ra0sms/nano-server/pics/nano-server-web-2-tile.jpg

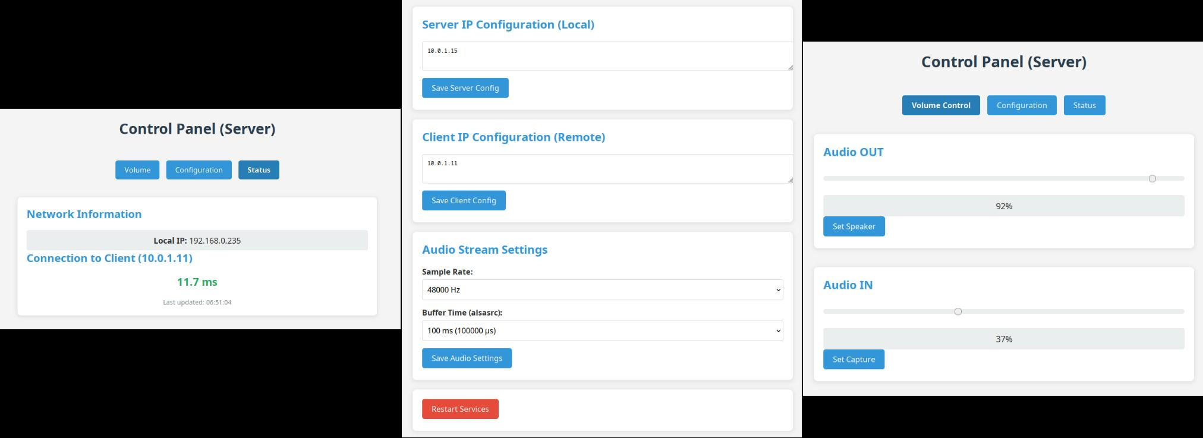
pics/nano-server-web-2-tile.jpg
