ra0sms/nano-server/pics/nano_server_3d.png

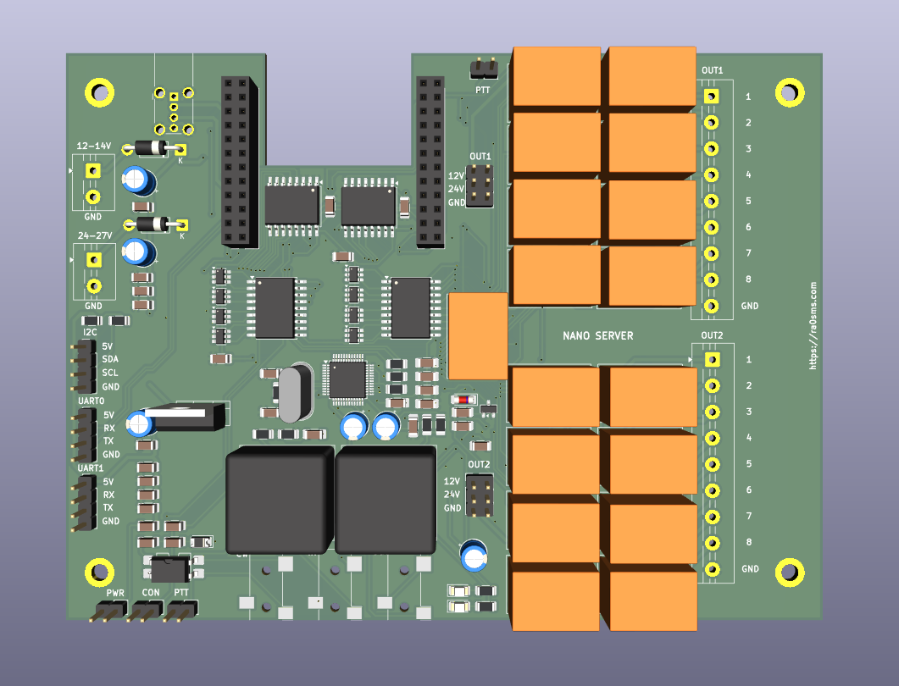
pics/nano_server_3d.png
