ra0sms/nano-server/pics/out-2.jpg

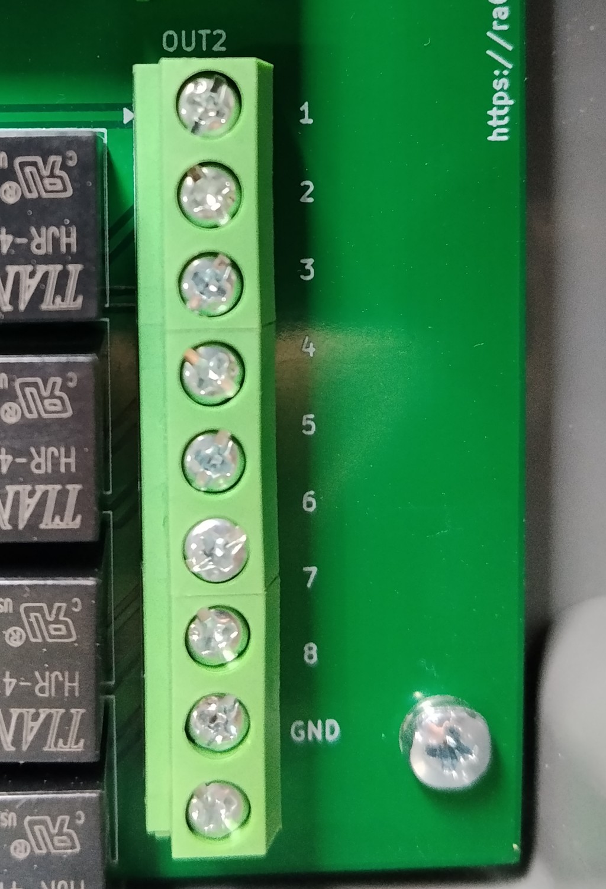
pics/out-2.jpg
